ybugge/Photobox/Resources/PageCameraPreview/CountDown/4.png

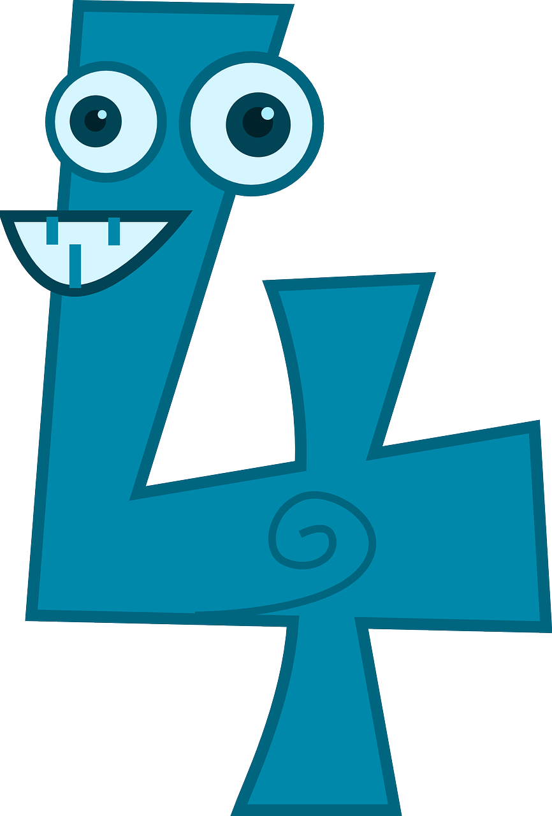
Resources/PageCameraPreview/CountDown/4.png
