ybugge/Photobox/Resources/PageCameraPreview/CountDown/5.png

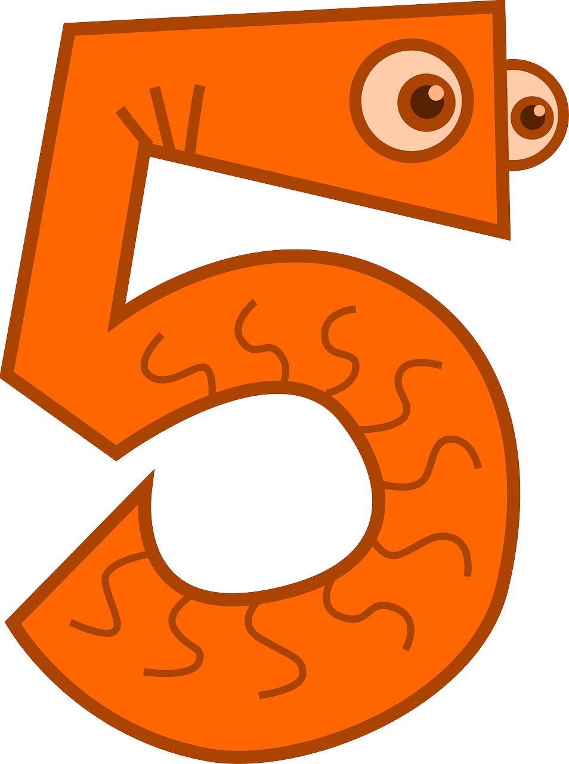
Resources/PageCameraPreview/CountDown/5.png
