ybugge/Photobox/Resources/PageTitlePicture/background.png

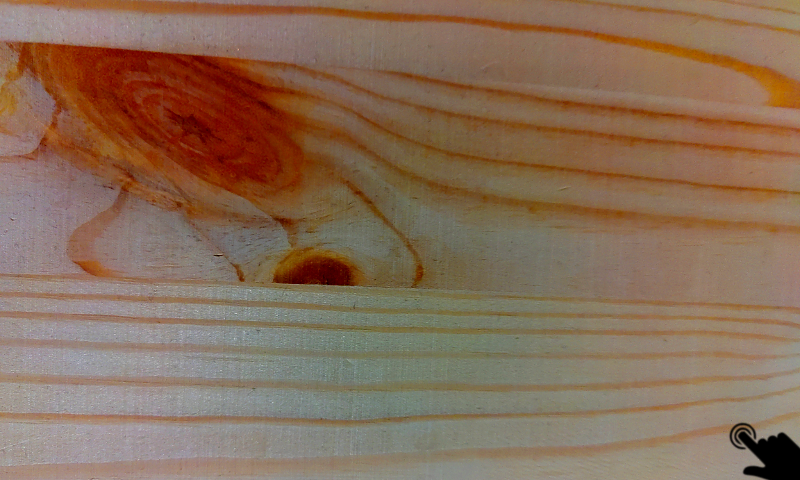
Resources/PageTitlePicture/background.png
