ybugge/Photobox/Resources/PageTitlePicture/Smiley/smile2.png

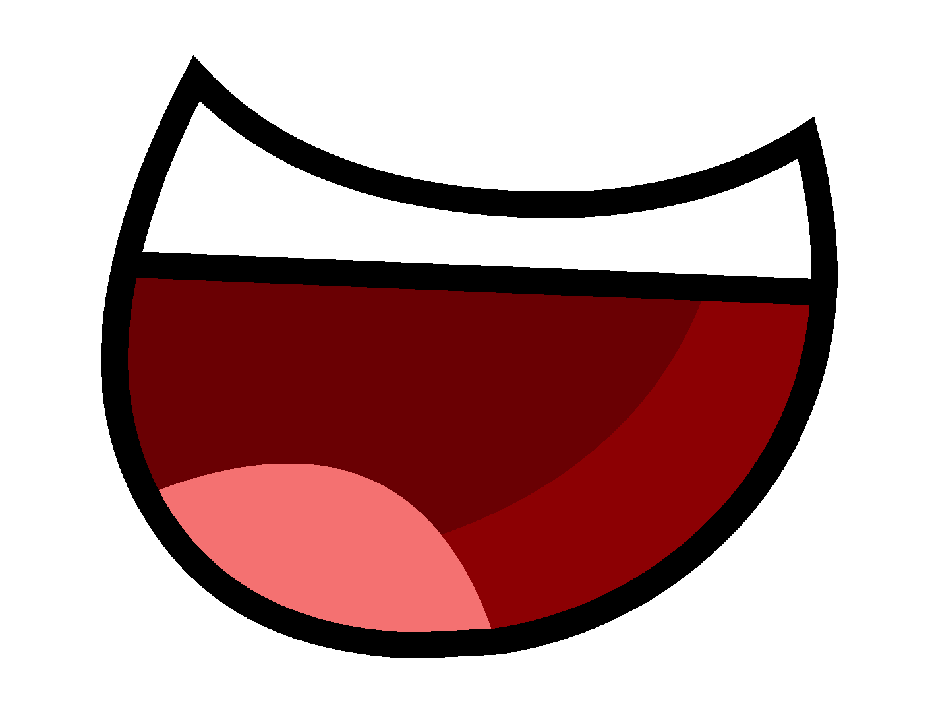
Resources/PageTitlePicture/Smiley/smile2.png
