ybugge/Photobox/Resources/PageTitlePicture/Smiley/smile4.png

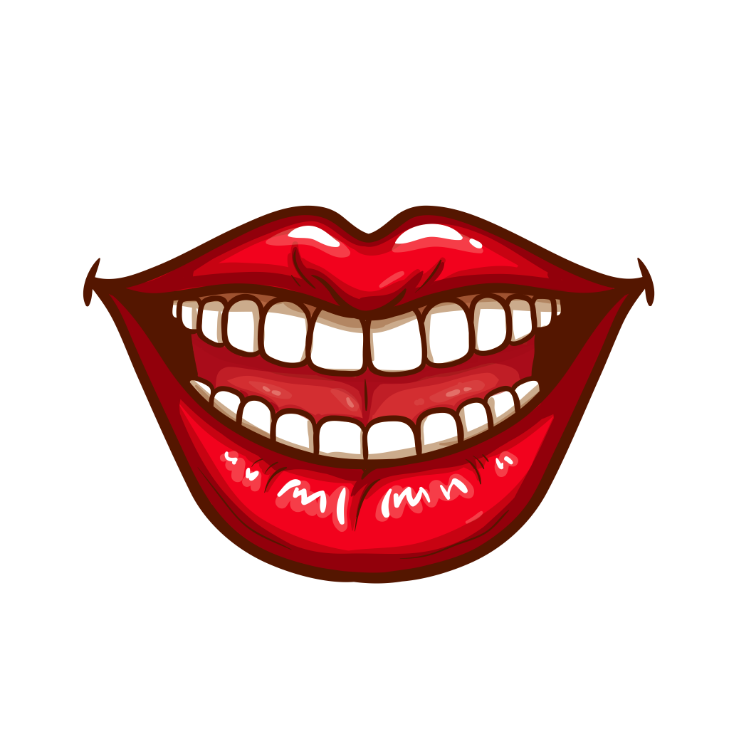
Resources/PageTitlePicture/Smiley/smile4.png
