ybugge/Photobox/Hardware/3dModels/Augen/Auge4_rechts.stl

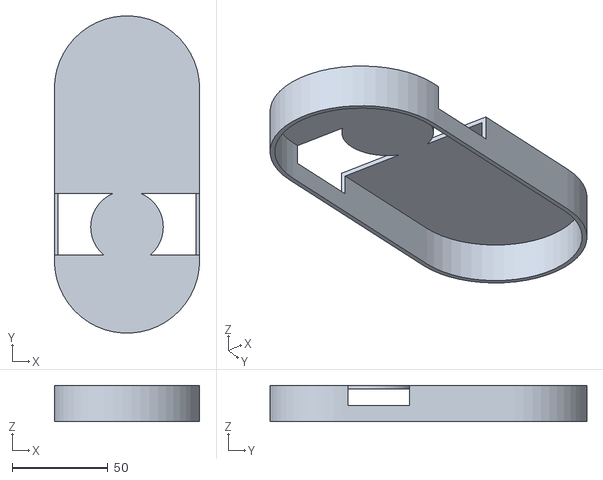
[picture p26: CAD file, 2021-07-10]
Hardware/3dModels/Augen/Auge4_rechts.stl
76.0 x 165.9 x 19.0
