ybugge/Photobox/Hardware/3dModels/Drucker/Drucker_Halter_Boden.stl

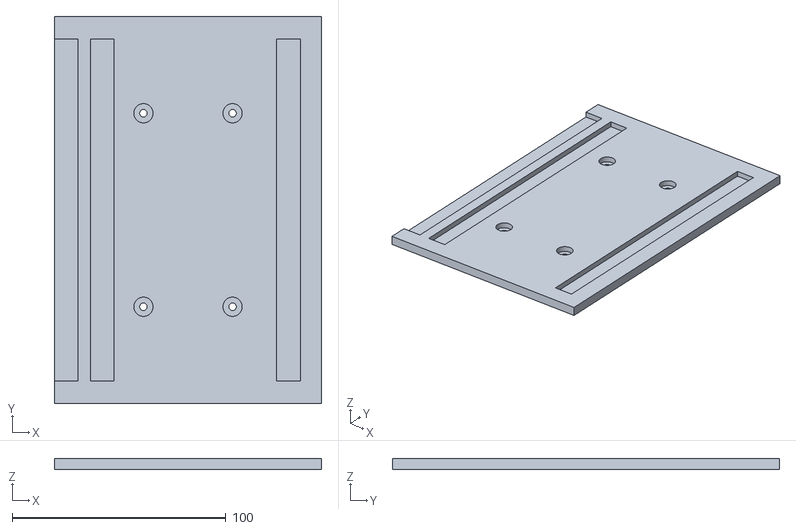
[picture p27: CAD file, 2021-07-10]
Hardware/3dModels/Drucker/Drucker_Halter_Boden.stl
125.0 x 181.0 x 5.00
