ybugge/Photobox/Hardware/3dModels/Kabelkanal/Kabelkanal_Deckel_seite_unten.stl

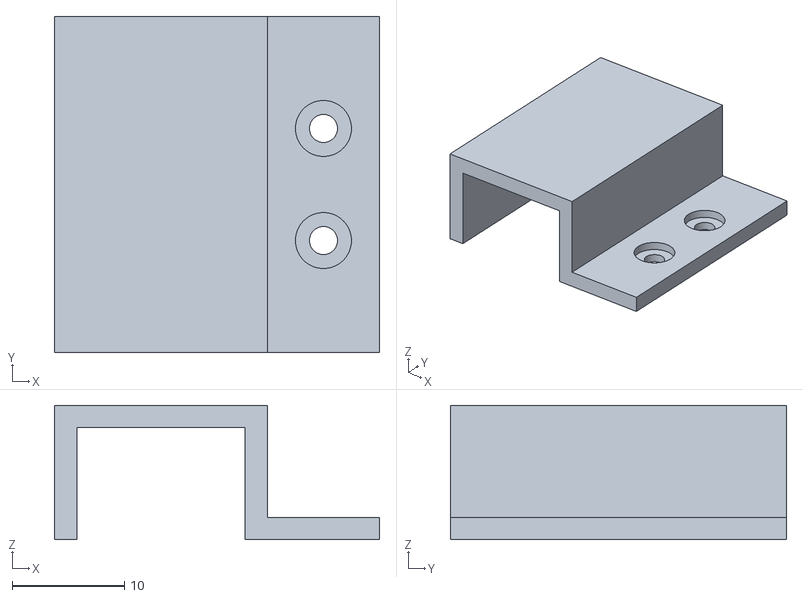
[picture p28: CAD file, 2021-07-10]
Hardware/3dModels/Kabelkanal/Kabelkanal_Deckel_seite_unten.stl
29.0 x 30.0 x 12.0
