ybugge/Photobox/Hardware/3dModels/Kamera/Kamera_halter.stl

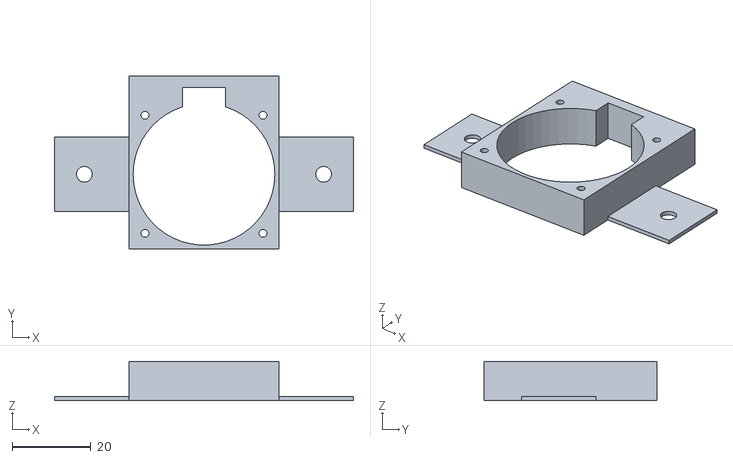
[picture p29: CAD file, 2021-07-10]
Hardware/3dModels/Kamera/Kamera_halter.stl
76.0 x 44.0 x 10.0
