ybugge/Photobox/Hardware/3dModels/Router/Router_Stuetzplatte.stl

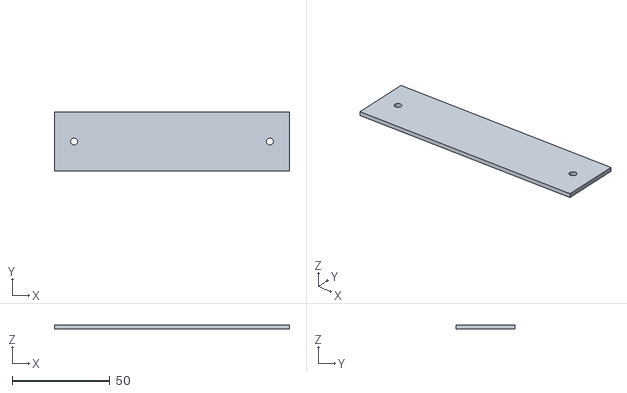
[picture p30: CAD file, 2021-07-10]
Hardware/3dModels/Router/Router_Stuetzplatte.stl
120.0 x 30.0 x 2.00
