ybugge/Photobox/Hardware/3dModels/Drucker/Drucker_PapierschlittenHalter.stl

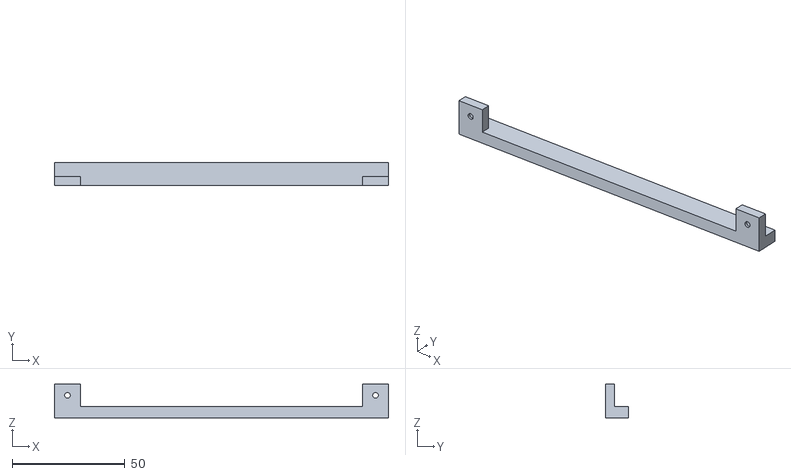
[picture p31: CAD file, 2021-07-10]
Hardware/3dModels/Drucker/Drucker_PapierschlittenHalter.stl
148.0 x 10.0 x 15.0
