ybugge/Photobox/Hardware/3dModels/Augen/Auge3_rechts.stl

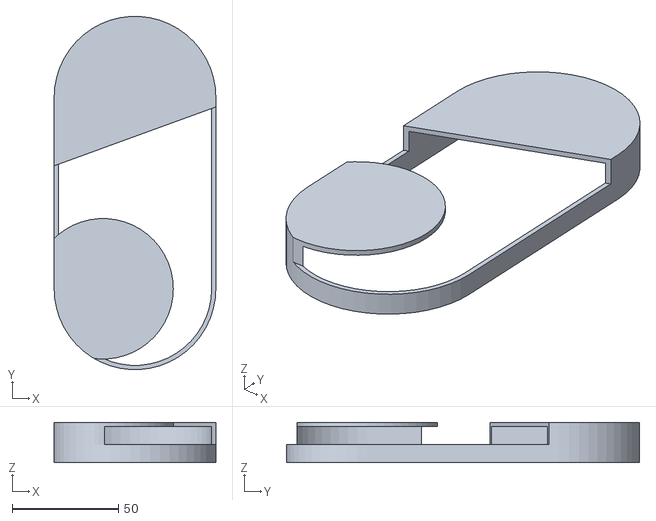
[picture p32: CAD file, 2021-07-10]
Hardware/3dModels/Augen/Auge3_rechts.stl
76.0 x 165.9 x 19.0
