ybugge/Photobox/Hardware/3dModels/Drucker/Drucker_Halter_Vorne.stl

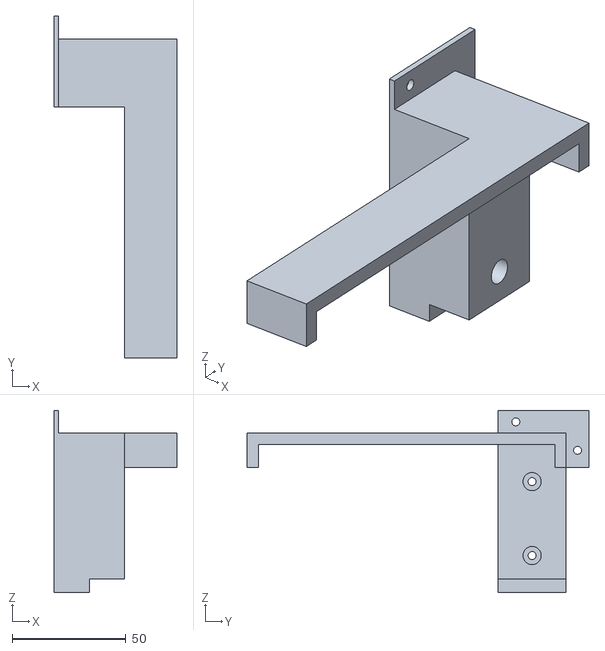
[picture p33: CAD file, 2021-07-10]
Hardware/3dModels/Drucker/Drucker_Halter_Vorne.stl
54.0 x 150.3 x 80.0
