ybugge/Photobox/Hardware/3dModels/Drucker/Drucker_PapierFuehrung.stl

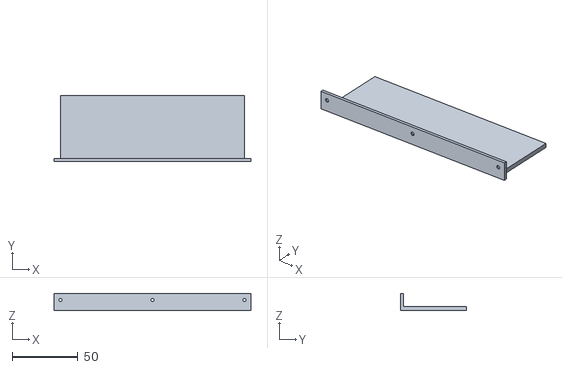
[picture p34: CAD file, 2021-07-10]
Hardware/3dModels/Drucker/Drucker_PapierFuehrung.stl
150.0 x 50.0 x 13.0
