ybugge/Photobox/Hardware/3dModels/Drucker/Drucker_Halter_Hinten.stl

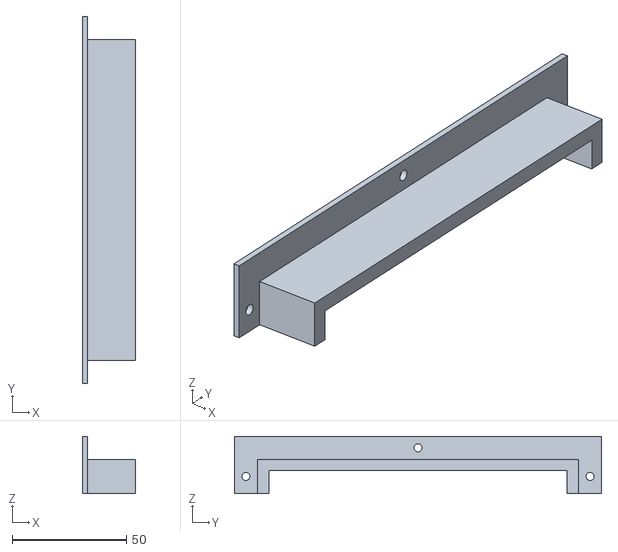
[picture p35: CAD file, 2021-07-10]
Hardware/3dModels/Drucker/Drucker_Halter_Hinten.stl
23.0 x 160.3 x 25.0
