ybugge/Photobox/Hardware/3dModels/Augen/Auge2_links.scad

include <../lib/Photobox.scad>;

eyes3();
