ybugge/Photobox/Hardware/3dModels/Augen/Auge2_rechts.scad

include <../lib/Photobox.scad>;

mirror([1,0,0])
eyes3();
