ybugge/Photobox/Hardware/3dModels/Augen/Auge3_links.scad

include <../lib/Photobox.scad>;

eyes4();
