ybugge/Photobox/Hardware/3dModels/Augen/Auge3_rechts.scad

include <../lib/Photobox.scad>;

mirror([1,0,0])
eyes4();
