ybugge/Photobox/Hardware/3dModels/Augen/Auge4_links.scad

include <../lib/Photobox.scad>;

eyes5();
