ybugge/Photobox/Hardware/3dModels/Augen/Auge4_rechts.scad

include <../lib/Photobox.scad>;

mirror([1,0,0])
eyes5();
