ybugge/Photobox/Hardware/3dModels/Display/Display_Halter_links.scad

include <../lib/Photobox.scad>;

rotate([180,0,0])
displayHolder();
