ybugge/Photobox/Hardware/3dModels/Display/Display_Halter_rechts.scad

include <../lib/Photobox.scad>;

rotate([180,0,0])
mirror([1,0,0])
displayHolder();
