ybugge/Photobox/Hardware/3dModels/Drucker/Drucker_Halter_Boden.scad

include <../lib/Photobox.scad>;

printerBottomHolder();
