ybugge/Photobox/Hardware/3dModels/Drucker/Drucker_Halter_Hinten.scad

include <../lib/Photobox.scad>;

printerSideHolder(0);
