ybugge/Photobox/Hardware/3dModels/Drucker/Drucker_Halter_Hinten_Stuetzplatte.scad

include <../lib/Photobox.scad>;

printerSideBackplate();
