ybugge/Photobox/Hardware/3dModels/Drucker/Drucker_Halter_Vorne.scad

include <../lib/Photobox.scad>;

printerSideHolder(31);
