ybugge/Photobox/Hardware/3dModels/Drucker/Drucker_PapierFuehrung.scad

include <../lib/Photobox.scad>;

printerTopPictureRail();
