ybugge/Photobox/Hardware/3dModels/Drucker/Drucker_PapierschachtCover.scad

include <../lib/Photobox.scad>;

printerFrontCoverSimple();
