ybugge/Photobox/Hardware/3dModels/Drucker/Drucker_PapierschlittenHalter.scad

include <../lib/Photobox.scad>;

paperHolder();
