ybugge/Photobox/Hardware/3dModels/Kabelkanal/Kabelkanal_Deckel_oben.scad

include <../lib/Photobox.scad>;

wireclamp(7,100,4,2);
