ybugge/Photobox/Hardware/3dModels/Kabelkanal/Kabelkanal_Deckel_seite_oben.scad

include <../lib/Photobox.scad>;

wireclamp(15,70,10,2);
