ybugge/Photobox/Hardware/3dModels/Kabelkanal/Kabelkanal_Deckel_seite_unten.scad

include <../lib/Photobox.scad>;

wireclamp(15,30,10,2);
