ybugge/Photobox/Hardware/3dModels/Kamera/Kamera_Abdeckung.scad

include <../lib/Photobox.scad>;

cameraCover();
