ybugge/Photobox/Hardware/3dModels/Kamera/Kamera_Abdeckung_hinten.scad

include <../lib/Photobox.scad>;

cameraBackCover();
