ybugge/Photobox/Hardware/3dModels/Kamera/Kamera_halter.scad

include <../lib/Photobox.scad>;

cameraBase();
