ybugge/Photobox/Hardware/3dModels/Router/Router_Mutter_Abdeckung.scad

include <../lib/Photobox.scad>;

routerHolderNutCover();
