ybugge/Photobox/Hardware/3dModels/Router/Router_Stuetzplatte.scad

include <../lib/Photobox.scad>;

routerHolderBackplate();
