ybugge/Photobox/Hardware/3dModels/Schnapper/Schnapper_Deckel_Distanzstueck_links.scad

include <../lib/Photobox.scad>;

mirror([1,0,0])
schnapperDistance();
