ybugge/Photobox/Hardware/3dModels/Schnapper/Schnapper_Deckel_Distanzstueck_rechts.scad

include <../lib/Photobox.scad>;

schnapperDistance();
