ybugge/Photobox/Hardware/3dModels/Stromanschluss/Stromanschluss_Abdeckung.scad

include <../lib/Photobox.scad>;

powerSupplyCover();
