ybugge/Photobox/Hardware/3dModels/Zwischenwand/Zwischenwand_Halter_hinten.scad

include <../lib/Photobox.scad>;

intermediateFloorMount(50,true);
