ybugge/Photobox/Hardware/3dModels/Zwischenwand/Zwischenwand_Halter_seite.scad

include <../lib/Photobox.scad>;

intermediateFloorMount(100,true);
